obbo-pl/pi-powerman/pi-powerman-hardware.yaml

#example hardware configuration file for pi-powerman.py
  
i2c:
    # 7 bit address (will be left shifted to add the read write bit)
    ADDRESS: 0x55
    RECEIVE_BUFFER_SIZE: 32
    SEND_BUFFER_SIZE: 32
    MAX_SEND_QUEUE: 128
    DROP_SEND_BUFFER_ON_FAILED: true

setup: 
    calibration_vin: 10403
    calibration_vbat: 9945
    on_boot_output: 'OUT4'
    on_boot_delay_s: 3
    on_down_delay_s: 5
    on_pioff_output: 'OUT4'
    on_pioff_delay_s: 3
    daemon_timeout_s: 120
    error_recoverable: 'TIMEOUT_DAEMON, DAEMON, BATTERY_OVERHEAT'
    ups_behavior: 'DELAYED'
    ups_shut_delay_s: 180
    ups_cut_level_mv: 8000 
    ups_min_charge_time_s: 30
    battery_overheat_01k: 33500
    main_power_loss_mv: 7000
    
outputs:
    ports:
        # available outputs and corresponding bit [0 - 7]
        OUT1: 0
        OUT2: 1
        OUT3: 2
        OUT4: 3
        OUT5: 4
        OUT6: 5
        OUT7: 6
        OUT8: 7
    state:
        - 'OFF'
        - 'ON'
        
daemon:
    state:
        - 'Running (level low)'
        - 'Power Off (high impedance)'
        - 'Running (level high)'

errors:
    - 'MAIN_CLOCK'
    - 'RTC_CLOCK'
    - 'INA219'
    - 'TIMEOUT_ADC'
    - 'DAEMON'
    - 'TIMEOUT_DAEMON'
    - 'SYSTEM'
    - 'BATTERY_OVERHEAT'

ups:
    state:
        - 'FAULT'
        - 'CHRG'
        - 'TOC'
        - 'READY'
        - 'CHRG_DISABLE'
        - 'DISCHARGE'
        - 'ON_BAT'

    behavior:
        # shutdown immediately
        - 'IMMEDIATELY' 
        # shutdown after <ups_shut_delay> second 
        - 'DELAYED'
        # shutdown when the battery voltage is lower than <ups_cut_level>
        - 'BATTERY' 
        
buttons:
    ports:
        # available buttons and corresponding byte
        PWR: 0
        SW1: 1
        SW2: 2
        SW3: 3
        SW4: 4
        SW5: 5
        SW6: 6
        SW7: 7
    state:
        - 'IDLE'
        - 'ON'
        - 'TURN_OFF_01'
        - 'TURN_OFF_02'
        - 'TURN_OFF_03'
        - 'TURN_OFF_04'
        - 'TURN_OFF_05'
        - 'OFF'
        - 'TURN_ON_01'
        - 'TURN_ON_02'
        - 'TURN_ON_03'
        - 'TURN_ON_04'
        - 'TURN_ON_05'
        - 'PRESS'
        - 'DISABLE'

requests:
    DAEMON_REQUEST_READ_INFO0: 0x41
    DAEMON_REQUEST_READ_INFO1: 0x42
    DAEMON_REQUEST_READ_INFO2: 0x43
    DAEMON_REQUEST_READ_INFO3: 0x44
    DAEMON_REQUEST_READ_STATUS: 0x45
    DAEMON_REQUEST_READ_SETUP: 0x46
    DAEMON_REQUEST_WRITE_SETUP: 0x47
    DAEMON_REQUEST_BUTTON: 0x48
    DAEMON_REQUEST_PRESS: 0x49
    DAEMON_REQUEST_OUTPUT: 0x4a
    DAEMON_REQUEST_KEEPALIVE: 0x4b
    DAEMON_REQUEST_ERROR: 0x4c
    DAEMON_REQUEST_CLEAR_ERROR: 0x4d
    DAEMON_REQUEST_SYSTEM: 0x4e
    DAEMON_REQUEST_DISABLE_CHARGE: 0x4f
    DAEMON_REQUEST_ENABLE_CHARGE: 0x50
    DAEMON_REQUEST_DISCHARGE_START: 0x51
    DAEMON_REQUEST_DISCHARGE_STOP: 0x52
